martinzemanek-dev/ghostlight/ghostlight_program_g030/Core/Src/i2c.c

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
/* Includes ------------------------------------------------------------------*/
#include "i2c.h"

/* USER CODE BEGIN 0 */
#include "gpio.h"

volatile int i2c_busy;
volatile int i2c_err;
/* USER CODE END 0 */

I2C_HandleTypeDef hi2c1;
DMA_HandleTypeDef hdma_i2c1_rx;
DMA_HandleTypeDef hdma_i2c1_tx;

/* I2C1 init function */
void MX_I2C1_Init(void)
{

  hi2c1.Instance = I2C1;
  hi2c1.Init.Timing = 0x00503D58;
  hi2c1.Init.OwnAddress1 = 0;
  hi2c1.Init.AddressingMode = I2C_ADDRESSINGMODE_7BIT;
  hi2c1.Init.DualAddressMode = I2C_DUALADDRESS_DISABLE;
  hi2c1.Init.OwnAddress2 = 0;
  hi2c1.Init.OwnAddress2Masks = I2C_OA2_NOMASK;
  hi2c1.Init.GeneralCallMode = I2C_GENERALCALL_DISABLE;
  hi2c1.Init.NoStretchMode = I2C_NOSTRETCH_DISABLE;
  if (HAL_I2C_Init(&hi2c1) != HAL_OK)
  {
    Error_Handler();
  }

  /** Configure Analogue filter
  */
  if (HAL_I2CEx_ConfigAnalogFilter(&hi2c1, I2C_ANALOGFILTER_ENABLE) != HAL_OK)
  {
    Error_Handler();
  }

  /** Configure Digital filter
  */
  if (HAL_I2CEx_ConfigDigitalFilter(&hi2c1, 0) != HAL_OK)
  {
    Error_Handler();
  }
}

void HAL_I2C_MspInit(I2C_HandleTypeDef* i2cHandle)
{

  GPIO_InitTypeDef GPIO_InitStruct = {0};
  RCC_PeriphCLKInitTypeDef PeriphClkInit = {0};
  if(i2cHandle->Instance==I2C1)
  {
  /** Initializes the peripherals clocks
  */
    PeriphClkInit.PeriphClockSelection = RCC_PERIPHCLK_I2C1;
    PeriphClkInit.I2c1ClockSelection = RCC_I2C1CLKSOURCE_PCLK1;
    if (HAL_RCCEx_PeriphCLKConfig(&PeriphClkInit) != HAL_OK)
    {
      Error_Handler();
    }

    __HAL_RCC_GPIOB_CLK_ENABLE();
    __HAL_RCC_GPIOA_CLK_ENABLE();
    /**I2C1 GPIO Configuration
    PB7     ------> I2C1_SDA
    PA9 [PA11]     ------> I2C1_SCL
    */
    GPIO_InitStruct.Pin = GPIO_PIN_7;
    GPIO_InitStruct.Mode = GPIO_MODE_AF_OD;
    GPIO_InitStruct.Pull = GPIO_NOPULL;
    GPIO_InitStruct.Speed = GPIO_SPEED_FREQ_LOW;
    GPIO_InitStruct.Alternate = GPIO_AF6_I2C1;
    HAL_GPIO_Init(GPIOB, &GPIO_InitStruct);

    GPIO_InitStruct.Pin = GPIO_PIN_9;
    GPIO_InitStruct.Mode = GPIO_MODE_AF_OD;
    GPIO_InitStruct.Pull = GPIO_NOPULL;
    GPIO_InitStruct.Speed = GPIO_SPEED_FREQ_LOW;
    GPIO_InitStruct.Alternate = GPIO_AF6_I2C1;
    HAL_GPIO_Init(GPIOA, &GPIO_InitStruct);

    /* I2C1 clock enable */
    __HAL_RCC_I2C1_CLK_ENABLE();

    /* I2C1 DMA Init */
    /* I2C1_RX Init */
    hdma_i2c1_rx.Instance = DMA1_Channel1;
    hdma_i2c1_rx.Init.Request = DMA_REQUEST_I2C1_RX;
    hdma_i2c1_rx.Init.Direction = DMA_PERIPH_TO_MEMORY;
    hdma_i2c1_rx.Init.PeriphInc = DMA_PINC_DISABLE;
    hdma_i2c1_rx.Init.MemInc = DMA_MINC_ENABLE;
    hdma_i2c1_rx.Init.PeriphDataAlignment = DMA_PDATAALIGN_BYTE;
    hdma_i2c1_rx.Init.MemDataAlignment = DMA_MDATAALIGN_BYTE;
    hdma_i2c1_rx.Init.Mode = DMA_NORMAL;
    hdma_i2c1_rx.Init.Priority = DMA_PRIORITY_LOW;
    if (HAL_DMA_Init(&hdma_i2c1_rx) != HAL_OK)
    {
      Error_Handler();
    }

    __HAL_LINKDMA(i2cHandle,hdmarx,hdma_i2c1_rx);

    /* I2C1_TX Init */
    hdma_i2c1_tx.Instance = DMA1_Channel2;
    hdma_i2c1_tx.Init.Request = DMA_REQUEST_I2C1_TX;
    hdma_i2c1_tx.Init.Direction = DMA_MEMORY_TO_PERIPH;
    hdma_i2c1_tx.Init.PeriphInc = DMA_PINC_DISABLE;
    hdma_i2c1_tx.Init.MemInc = DMA_MINC_ENABLE;
    hdma_i2c1_tx.Init.PeriphDataAlignment = DMA_PDATAALIGN_BYTE;
    hdma_i2c1_tx.Init.MemDataAlignment = DMA_MDATAALIGN_BYTE;
    hdma_i2c1_tx.Init.Mode = DMA_NORMAL;
    hdma_i2c1_tx.Init.Priority = DMA_PRIORITY_LOW;
    if (HAL_DMA_Init(&hdma_i2c1_tx) != HAL_OK)
    {
      Error_Handler();
    }

    __HAL_LINKDMA(i2cHandle,hdmatx,hdma_i2c1_tx);

    /* I2C1 interrupt Init */
    HAL_NVIC_SetPriority(I2C1_IRQn, 0, 0);
    HAL_NVIC_EnableIRQ(I2C1_IRQn);
  }
}

void HAL_I2C_MspDeInit(I2C_HandleTypeDef* i2cHandle)
{

  if(i2cHandle->Instance==I2C1)
  {
    /* Peripheral clock disable */
    __HAL_RCC_I2C1_CLK_DISABLE();

    /**I2C1 GPIO Configuration
    PB7     ------> I2C1_SDA
    PA9 [PA11]     ------> I2C1_SCL
    */
    HAL_GPIO_DeInit(GPIOB, GPIO_PIN_7);

    HAL_GPIO_DeInit(GPIOA, GPIO_PIN_9);

    /* I2C1 DMA DeInit */
    HAL_DMA_DeInit(i2cHandle->hdmarx);
    HAL_DMA_DeInit(i2cHandle->hdmatx);

    /* I2C1 interrupt Deinit */
    HAL_NVIC_DisableIRQ(I2C1_IRQn);
  }
}

/* USER CODE BEGIN 1 */
void HAL_I2C_MasterTxCpltCallback(I2C_HandleTypeDef *hi2c) {
    if (hi2c->Instance == I2C1) {
        i2c_busy = 0; // This "unlocks" the while loop above
    }
}

void HAL_I2C_MasterRxCpltCallback(I2C_HandleTypeDef *hi2c) {
    if (hi2c->Instance == I2C1) {
        i2c_busy = 0; // This "unlocks" the while loop above
    }
}

void HAL_I2C_ErrorCallback(I2C_HandleTypeDef *hi2c) {
    if (hi2c->Instance == I2C1) {
    	i2c_busy = 0; // This "unlocks" the while loop above
    	i2c_err = hi2c->ErrorCode;
    }
}

/* USER CODE END 1 */
